pzfreo/whistle-key/drawings/titanium/frame-machining-review.pdf

SCOPE AND PROPOSED FINISH

1 QUOTATION / DFM REVIEW ONLY - NOT RELEASED FOR MACHINING.

2 Units mm. Do not scale. Read with sheet 2 and frame-reference.step.

3 One-piece lower frame; caps, keys, pads and hardware excluded.

4 CNC mill/drill from solid. Sheet profile cutting alone is insufficient.

5 Material: titanium; grade and stock condition to be agreed.

6 Nominal geometry retained from PETG prototype d24a674.

7 Proposed general linear tolerance +/-0.10; angles +/-0.5 deg.

8 Functional fits on sheet 2 override general proposal; confirm before release.

9 Deburr all edges. Proposed edge break 0.10-0.20 except fits/stops.

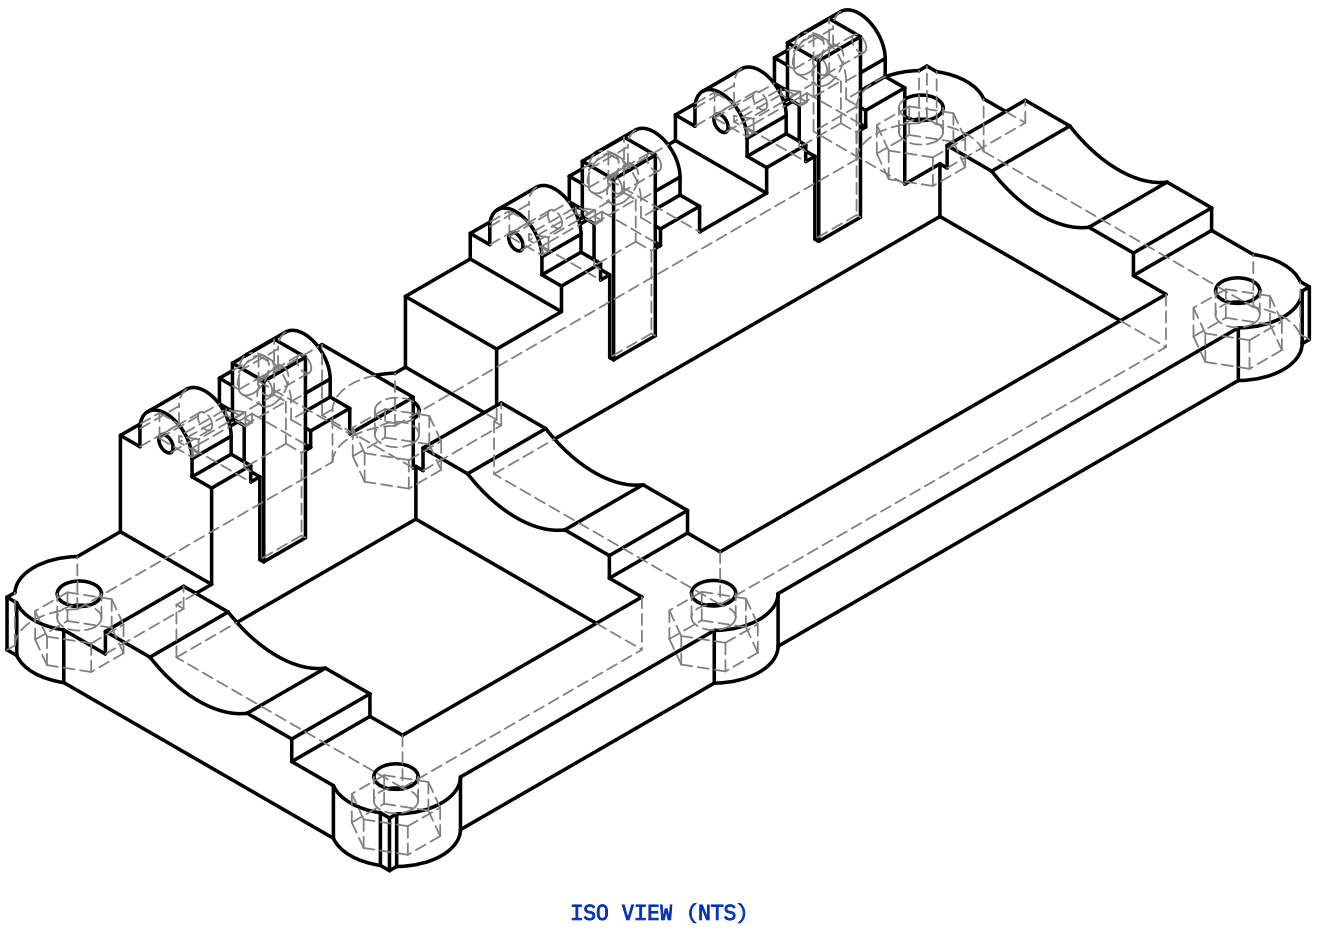
[picture p8: figure]
ISO VIEW (NTS)

10 Whistle seats: proposed Ra 1.6 um; no burrs or tool ridges.

11 Protect spring seats, stop faces and bearing lands from edge breaks.

12 CAD defines unlisted contours; all sharp internal corners need DFM review.

13 Section A-A: foot-end clamp at Y=0. Pocket floor Z=1.90.

14 Base top Z=3.50; nominal nut-pocket roof thickness 1.60.

A | A

31.3

15.3

71.6

SECTION A–A

RELEASE HOLDS

1 HOLD 1: confirm hole 5/6 measurements and resulting key positions.

2 HOLD 2: 1.10 CAD pin bores are a PRINT allowance, not a metal friction fit.

3 Agree pin retention and bore limits using actual 1 x 12 steel pins.

4 HOLD 3: six sharp hex pockets need EDM/broaching or approved relief.

5 No unapproved cutter radii in key sweeps, seats or nut corners.

6 HOLD 4: confirm titanium grade, clamp fit and all proposed tolerances.

7 A geometry drawing does not establish titanium clamp compliance.

FRAME / MACHINING REVIEW | WK-TI-001-1 | 2:1 | Ti / TBD | P1
DRAFT / SEE NOTES | | PZFREO / draftwright (https://github.com/pzfreo/draftwright)

FEATURE | X | Y | Z / DIRECTION
Clamp 1: 2 bolts / nut pockets +/-12.150 0.000 | Z axis
Clamp 2: 2 bolts / nut pockets +/-12.150 24.375 | Z axis
Clamp 3: 2 bolts / nut pockets +/-12.150 64.595 | Z axis
Key 4: spring socket | -9.800 | 53.595 | 13.700 / +X
Key 5: spring socket | -9.800 | 37.850 | 13.700 / +X
Key 6: spring socket | -9.800 | 11.000 | 13.700 / +X
Key 4: paired hinge bores | -11.200 | 53.595 +/- 3.800 11.100 / Y
Key 5: paired hinge bores | -11.200 | 37.850 +/- 3.800 11.100 / Y
Key 6: paired hinge bores | -11.200 | 11.000 +/- 3.800 11.100 / Y

6× ø 2.4 THRU

31.3

15.3

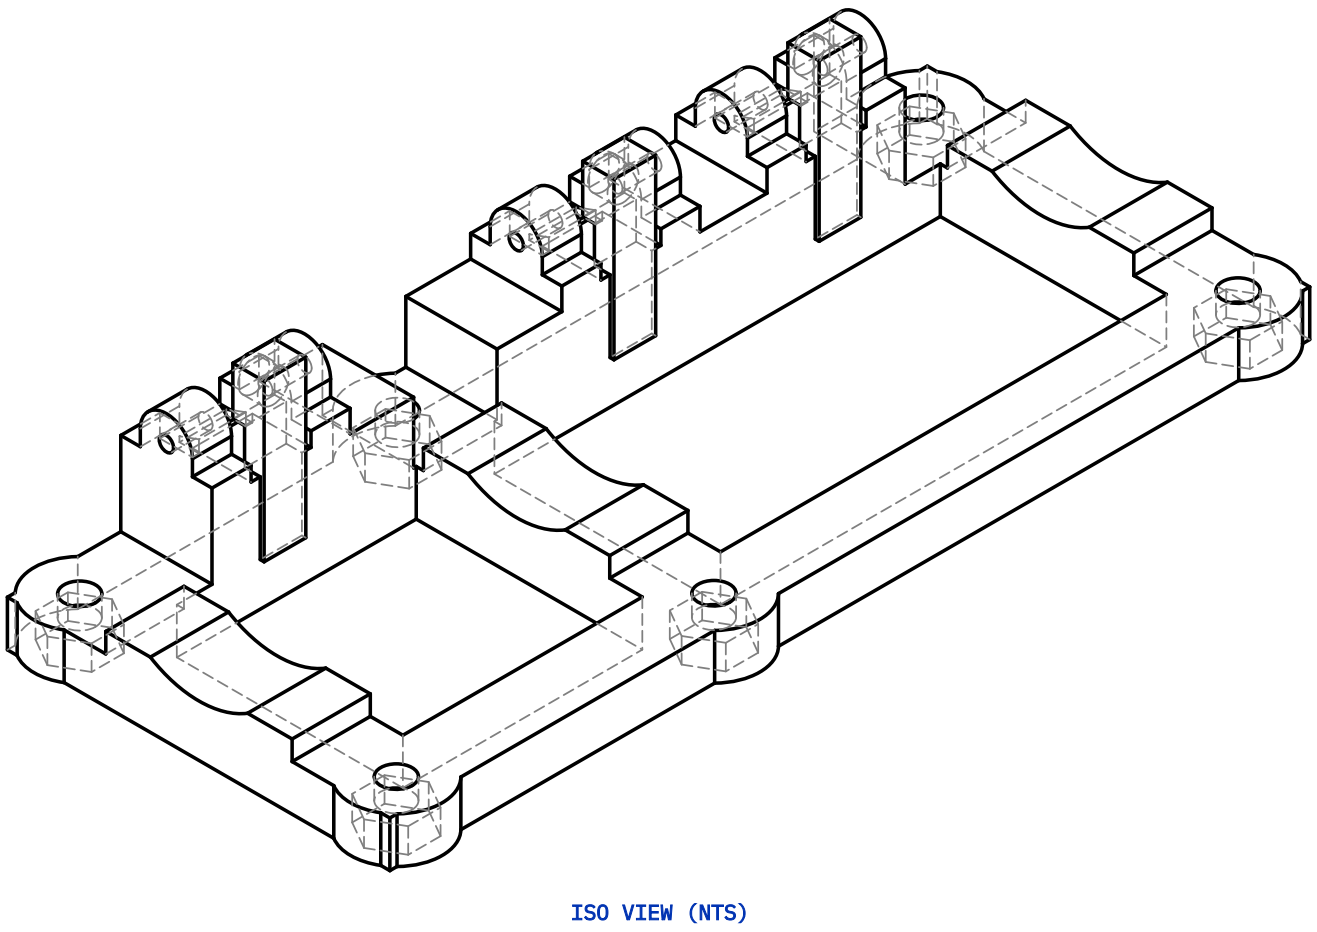
[picture p9: figure]
ISO VIEW (NTS)

3× ø 2.4

FEATURE DEFINITIONS / PROPOSED FITS

1 Coordinate origin: X=whistle axis; Y=foot-end clamp centre; Z=base.

2 +Y points toward mouthpiece. All coordinates match supplied STEP.

3 6 bolt holes: diameter 2.40 THRU; proposed +0.05 / -0.00.

4 6 nut pockets from underside: 4.30 AF x 1.90 deep; proposal +/-0.05.

5 Nut pocket flat normals parallel X. Nominal nut 4.00 AF x 1.60.

6 Pocket roof Z=1.90; lug top Z=3.50; roof thickness 1.60.

7 3 spring sockets: diameter 2.40 x 1.50 full-diameter depth.

8 Socket floor X=-8.300; flat floor required, drill tip not included.

9 6 hinge bores: CAD diameter 1.10 through 3.00-thick ears; FIT ON HOLD.

10 Each hinge pair: 4.60 clear axial gap; 10.60 outer span.

11 Common hinge axis X=-11.200, Z=11.100. Verify all six coaxial.

12 3 whistle seats: R7.150, axis X=0 / Z=11.100, axial width 6.00.

13 Seat radius proposed +/-0.02; all seats share one axis.

14 Key spacing 4-5=15.745 / 5-6=26.850 nominal; MEASUREMENT HOLD.

6× ø 1.1 THRU | 71.6
FRAME / FEATURE SCHEDULE | WK-TI-001-2 | 2:1 | Ti / TBD | P1
DRAFT / SEE NOTES | | PZFREO / draftwright (https://github.com/pzfreo/draftwright)
