pzfreo/whistle-key/docs/curved-key-layout.png

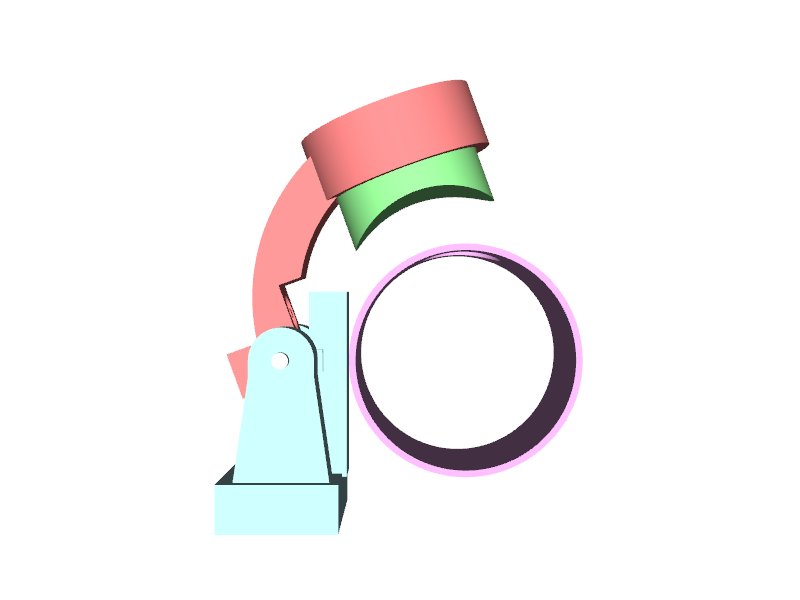
docs/curved-key-layout.png
