pzfreo/whistle-key/docs/eva-pad-and-template.png

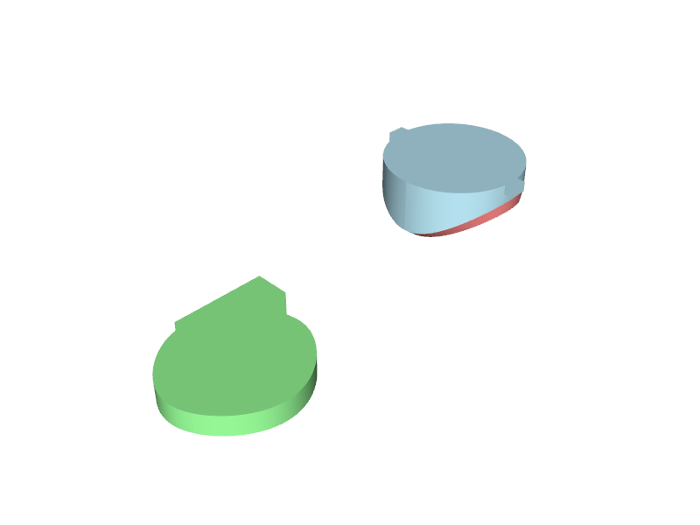
docs/eva-pad-and-template.png
