pzfreo/whistle-key/docs/hinge-reinforced.png

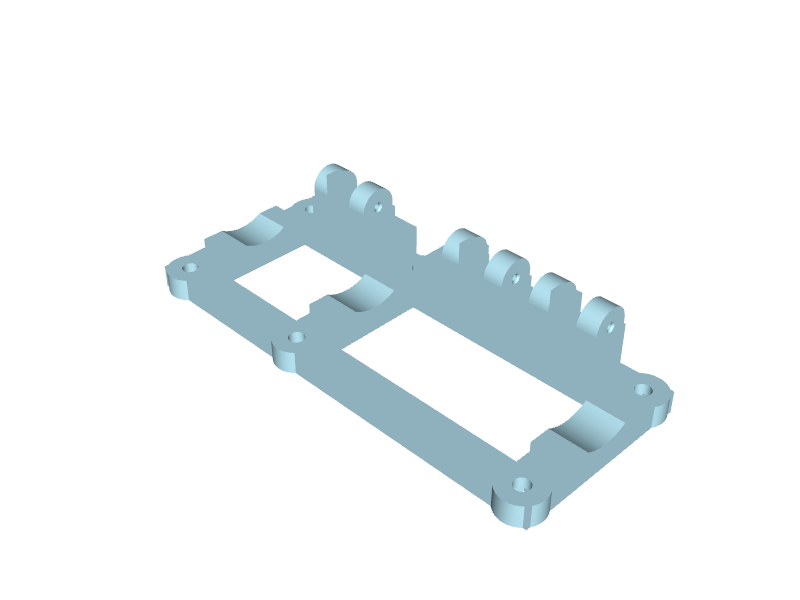
docs/hinge-reinforced.png
