pzfreo/whistle-key/docs/joined-pillars.png

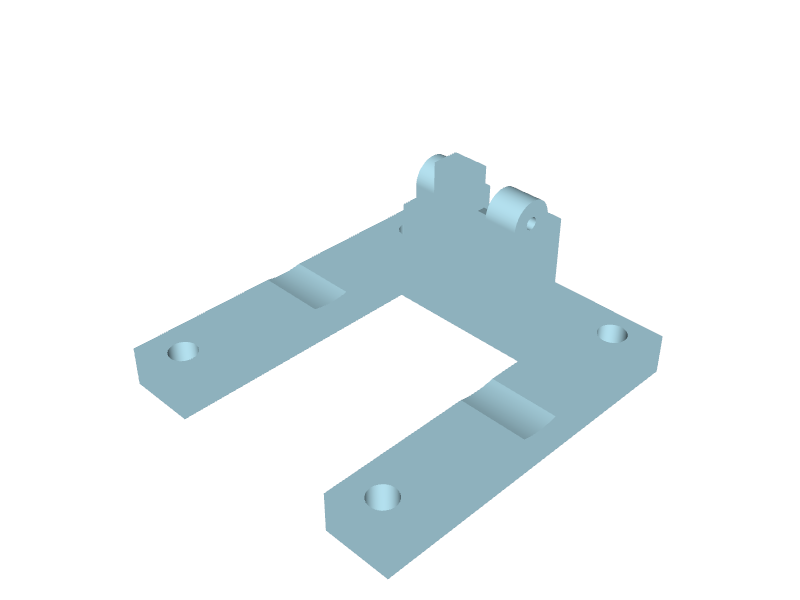
docs/joined-pillars.png
