pzfreo/whistle-key/docs/key-arm-reinforcement.png

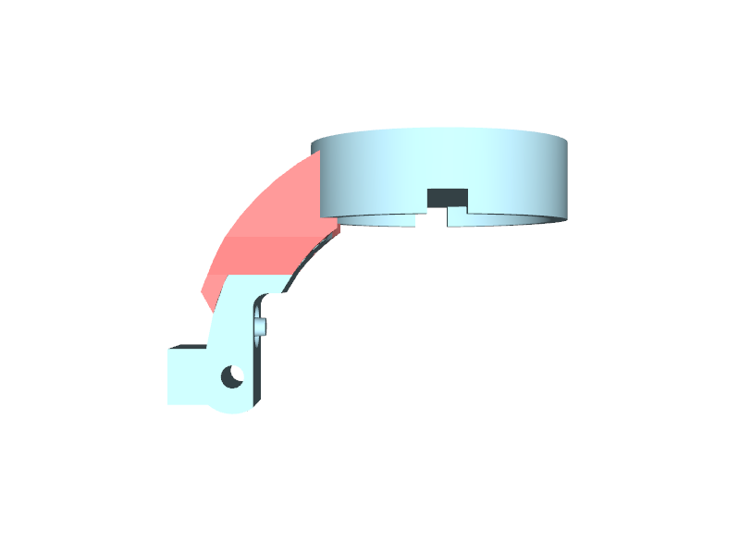
docs/key-arm-reinforcement.png
