pzfreo/whistle-key/docs/reinforced-pillars.png

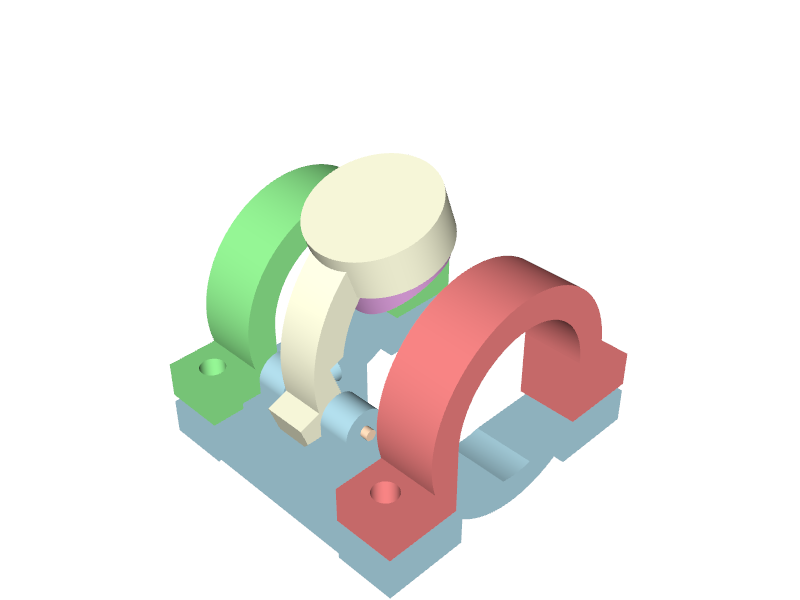
docs/reinforced-pillars.png
