pzfreo/whistle-key/docs/single-key.png

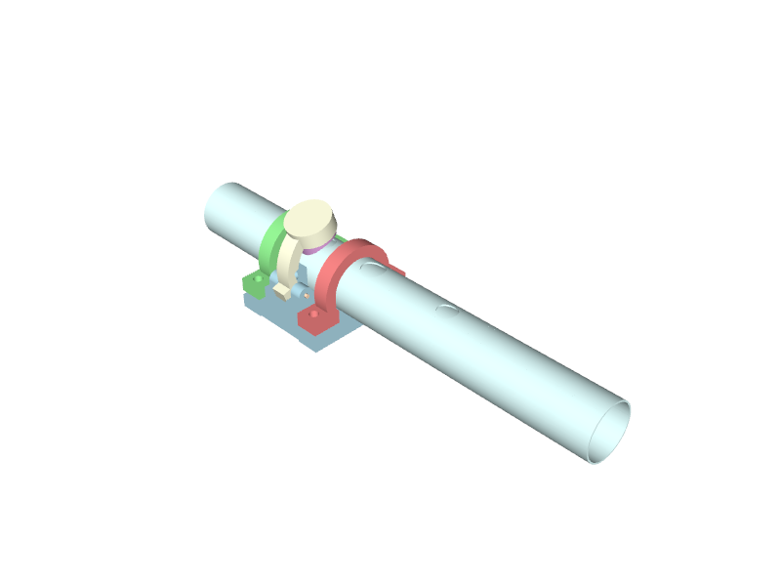
docs/single-key.png
