pzfreo/whistle-key/docs/spring-holder-flush.png

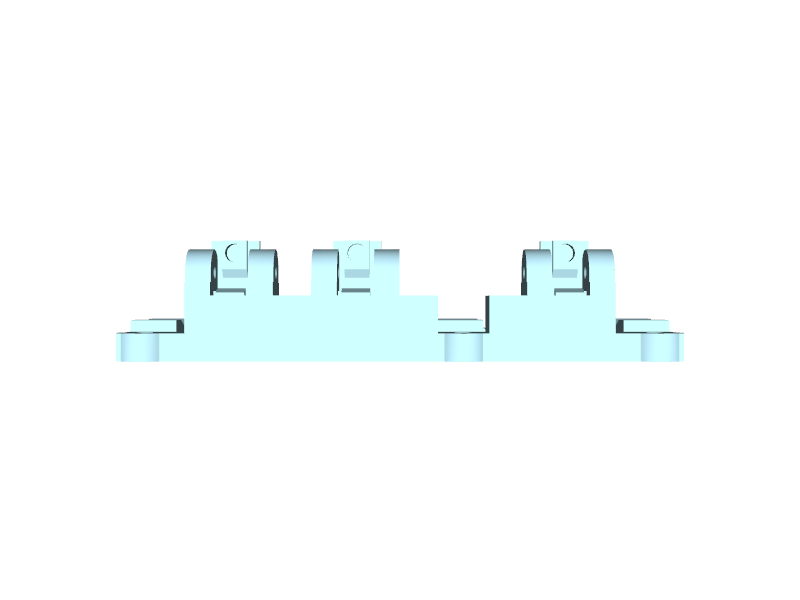
docs/spring-holder-flush.png
