pzfreo/whistle-key/docs/spring-socket-section.png

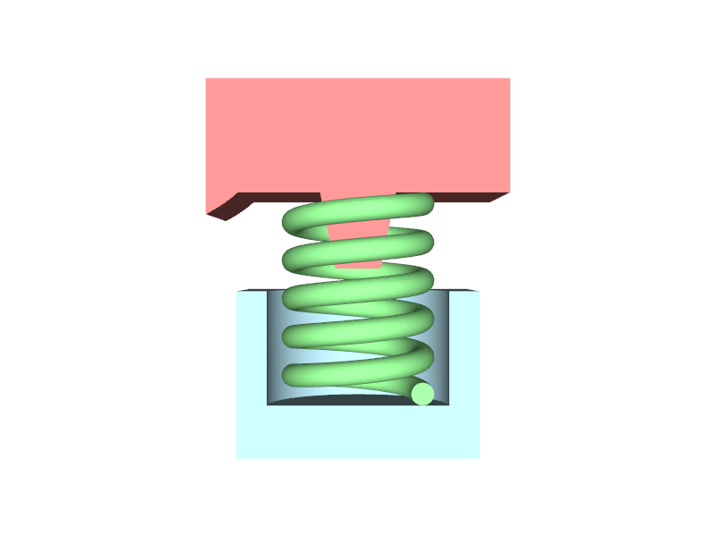
docs/spring-socket-section.png
