pzfreo/whistle-key/docs/tpu-continuous-face.png

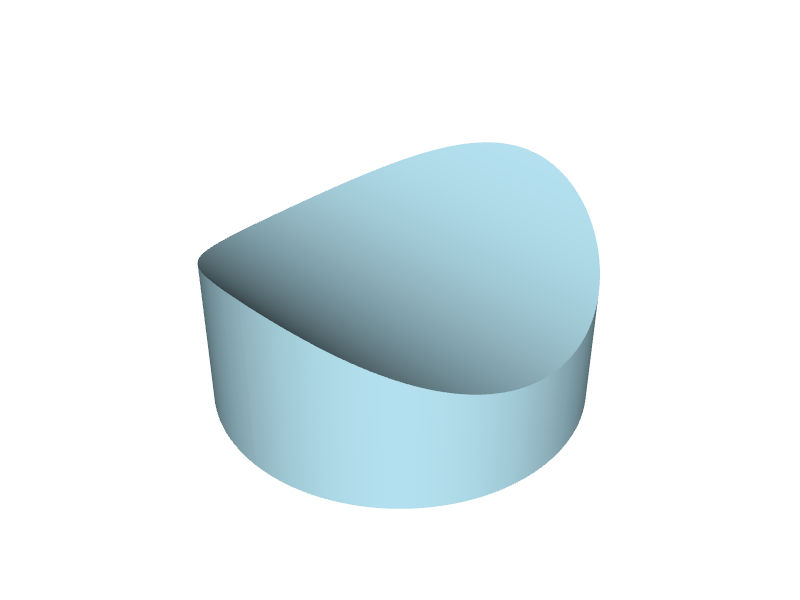
docs/tpu-continuous-face.png
