pzfreo/whistle-key/exports/three-key/print-oriented/frame_print.step

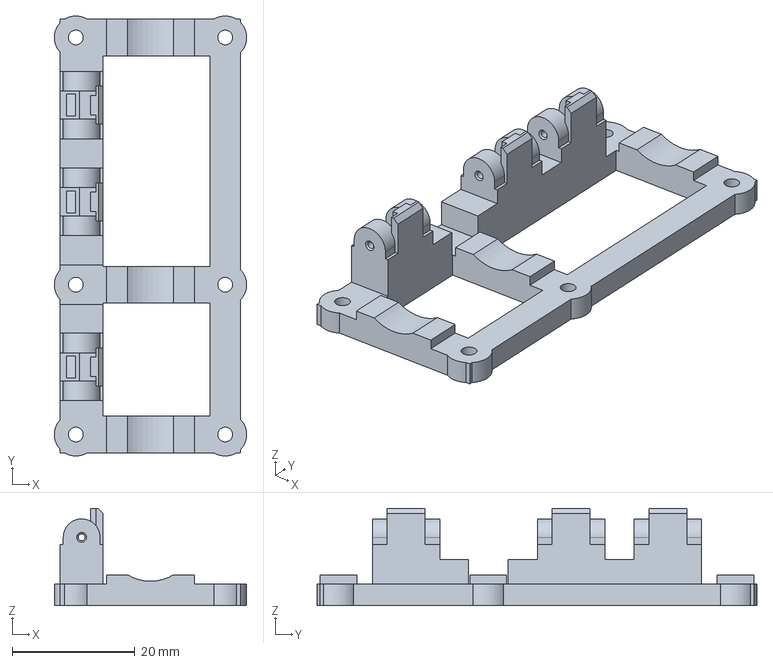
[picture p39: CAD file, 2026-09-13]
exports/three-key/print-oriented/frame_print.step
31.3 x 71.6 x 15.8 mm
