pzfreo/whistle-key/exports/three-key/whistle-three-key-P1S.3mf

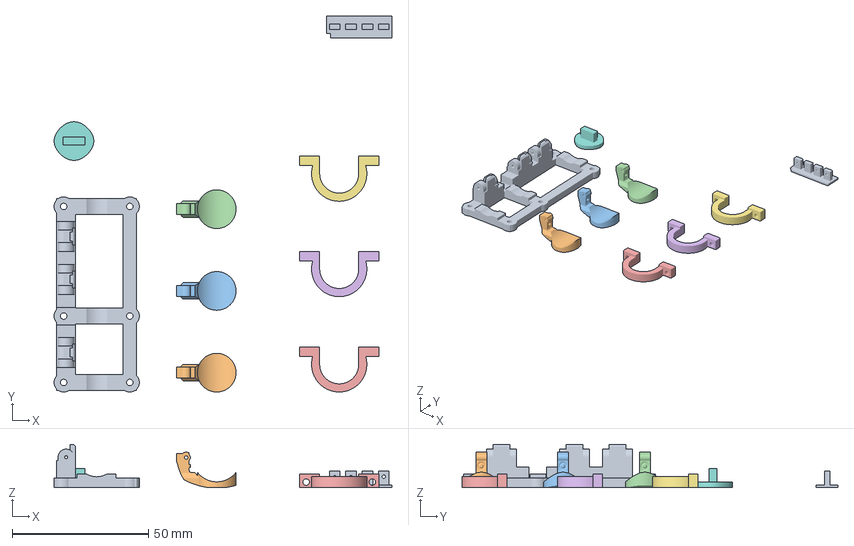
[picture p40: CAD file, 2026-09-13]
exports/three-key/whistle-three-key-P1S.3mf
124.0 x 138.0 x 15.8 mm
Three-key frame - flat base down
Common key 1 - finger face down
Common key 2 - finger face down
Common key 3 - finger face down
Clamp cap 1 - end face down
Clamp cap 2 - end face down
Clamp cap 3 - end face down
EVA liner cutting guide - flat base down
Pin fit coupon
