pzfreo/whistle-key/drawings/titanium/frame-general.dxf

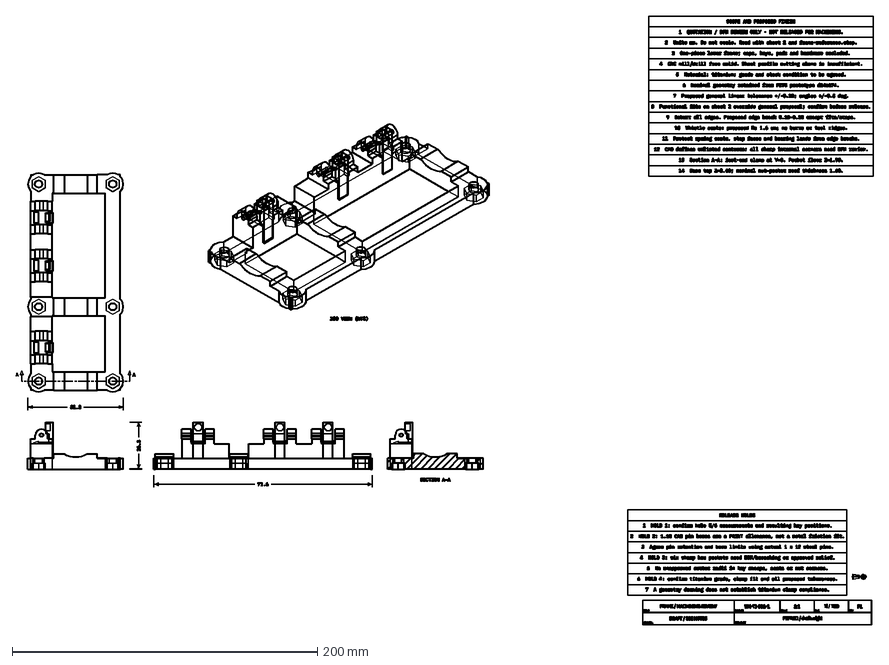
[picture p41: CAD file, 2026-09-08]
drawings/titanium/frame-general.dxf
561.8 x 399.1 mm
