pzfreo/whistle-key/exports/clamp_cap_0.step

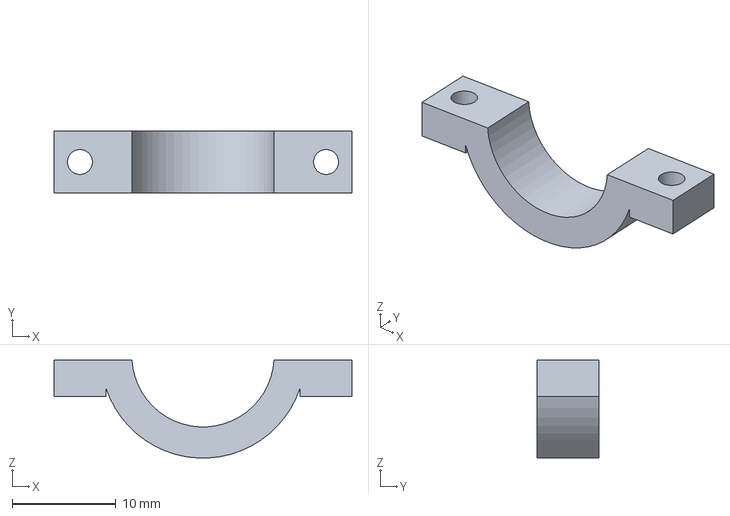
[picture p42: CAD file, 2026-09-06]
exports/clamp_cap_0.step
28.7 x 6.00 x 9.44 mm
