pzfreo/whistle-key/exports/single-key/frame.step

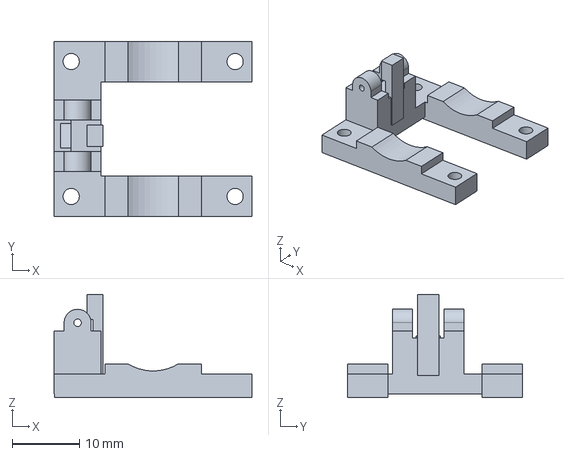
[picture p43: CAD file, 2026-09-08]
exports/single-key/frame.step
29.4 x 26.0 x 15.3 mm
