pzfreo/whistle-key/exports/three-key/print-oriented/lever_print.step

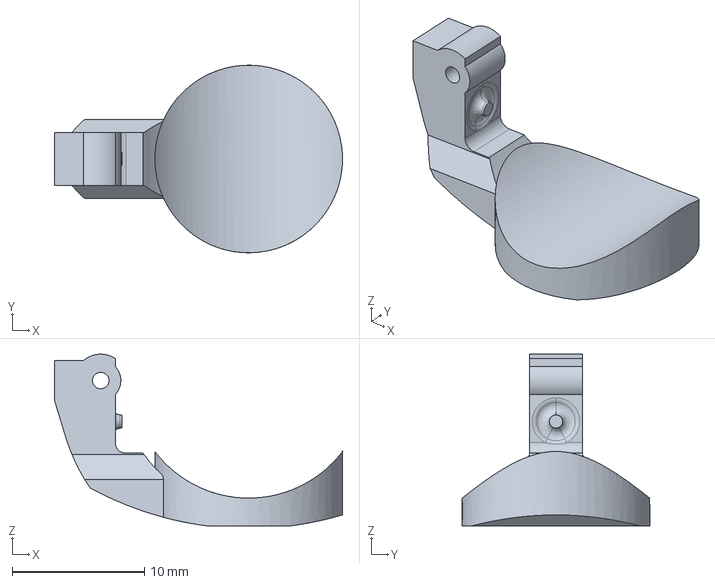
[picture p44: CAD file, 2026-09-13]
exports/three-key/print-oriented/lever_print.step
21.8 x 14.2 x 13.0 mm
