pzfreo/whistle-key/exports/single-key/print-oriented/tpu_pad_print.step

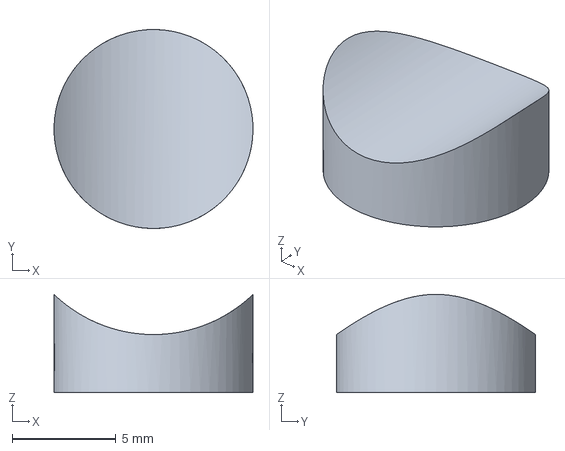
[picture p45: CAD file, 2026-09-08]
exports/single-key/print-oriented/tpu_pad_print.step
9.59 x 9.59 x 4.74 mm
