pzfreo/whistle-key/exports/single-key/whistle-key-P1S-dry-fit-PETG.3mf

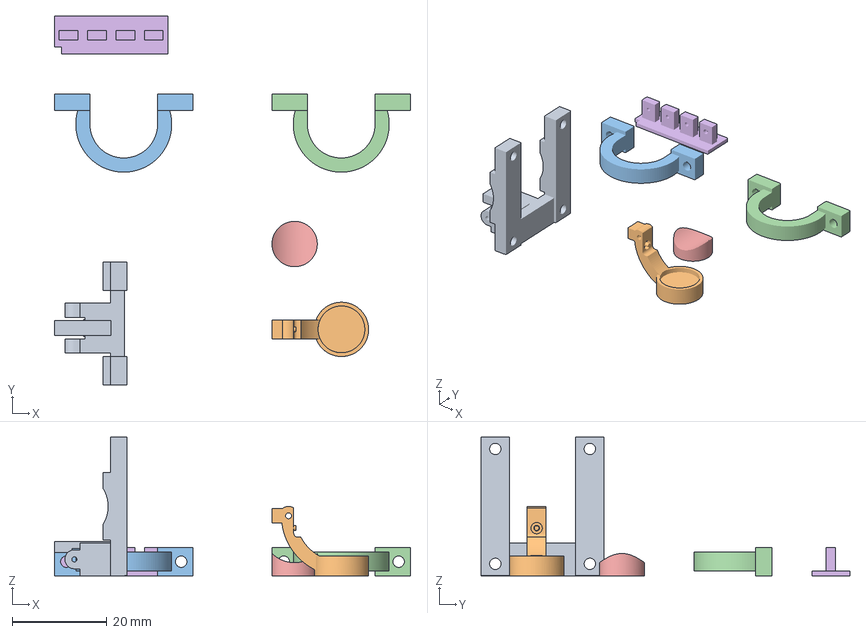
[picture p46: CAD file, 2026-09-08]
exports/single-key/whistle-key-P1S-dry-fit-PETG.3mf
75.3 x 78.0 x 29.4 mm
Frame - outer rail side down
Key - finger face down
Clamp cap 1 - end face down
Clamp cap 2 - end face down
Rigid pad - PETG dry fit
Pin fit coupon
