pzfreo/whistle-key/exports/three-key/print-oriented/pin_fit_coupon.step

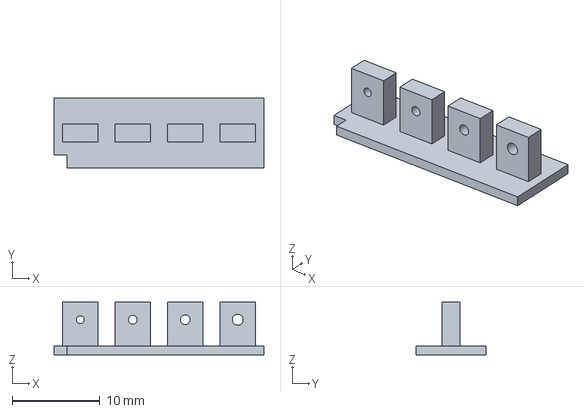
[picture p48: CAD file, 2026-09-13]
exports/three-key/print-oriented/pin_fit_coupon.step
24.0 x 8.00 x 6.00 mm
