pzfreo/whistle-key/exports/single-key/clamp_cap_0.step

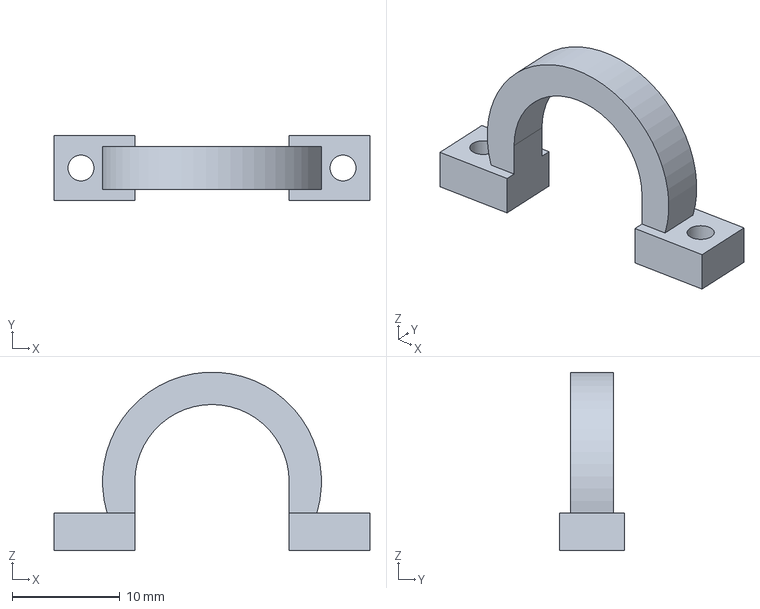
[picture p49: CAD file, 2026-09-08]
exports/single-key/clamp_cap_0.step
29.3 x 6.00 x 16.5 mm
