pzfreo/whistle-key/exports/single-key/lever_blank.step

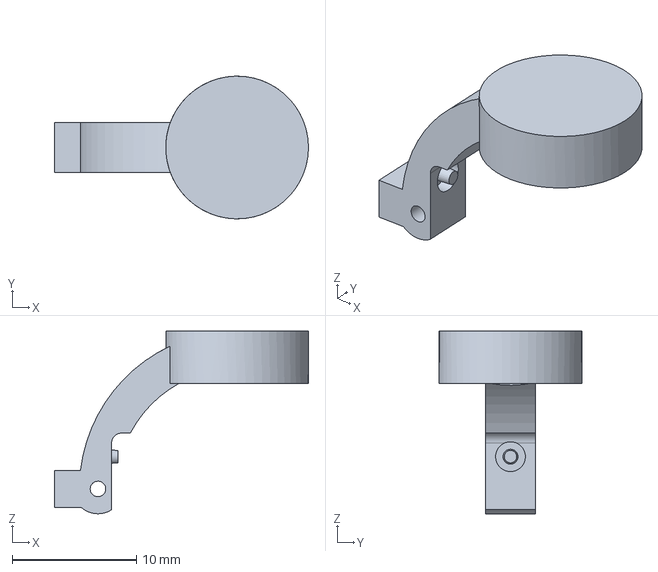
[picture p50: CAD file, 2026-09-08]
exports/single-key/lever_blank.step
20.4 x 11.5 x 14.7 mm
