pzfreo/whistle-key/docs/print-orientations.png

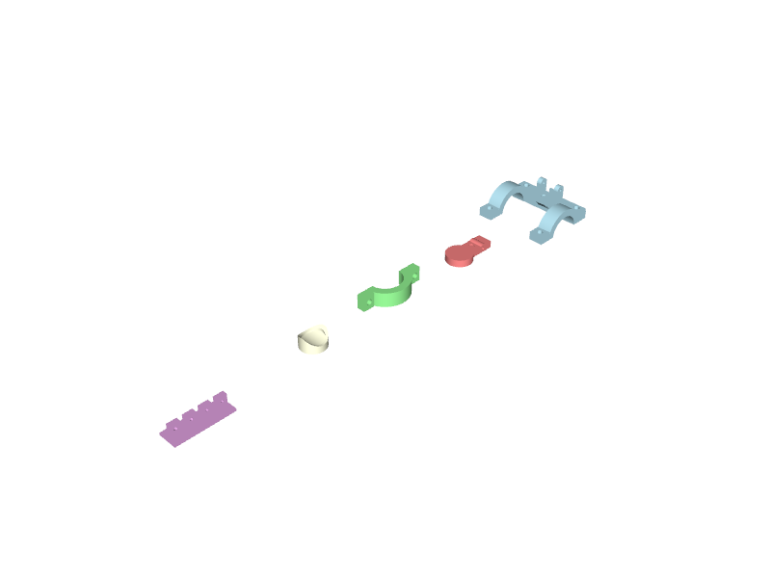
docs/print-orientations.png
